MCJack123/PSG/images/image1.jpg

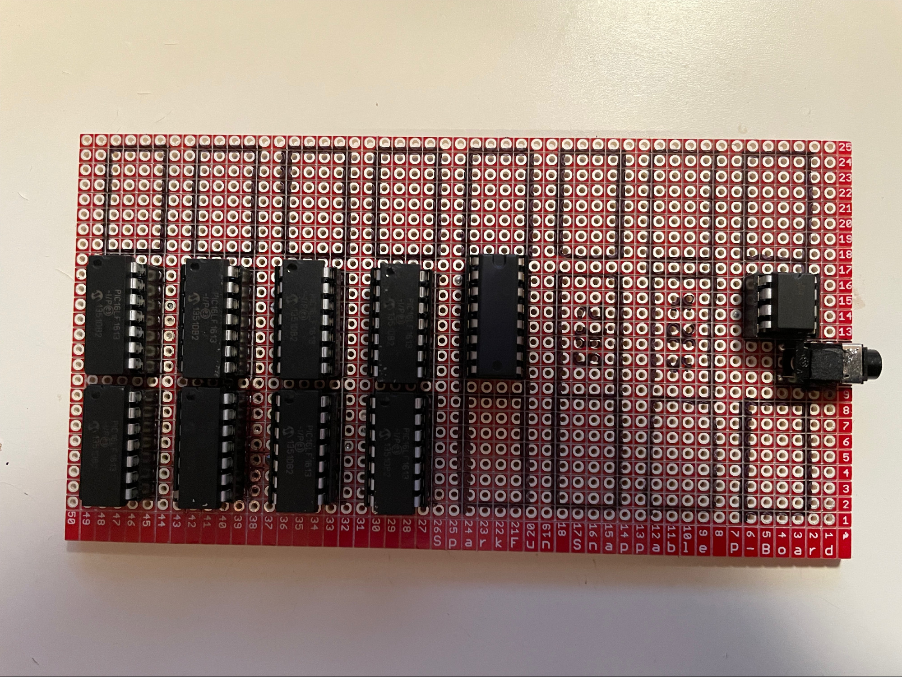
images/image1.jpg
