MCJack123/PSG/images/image2.jpg

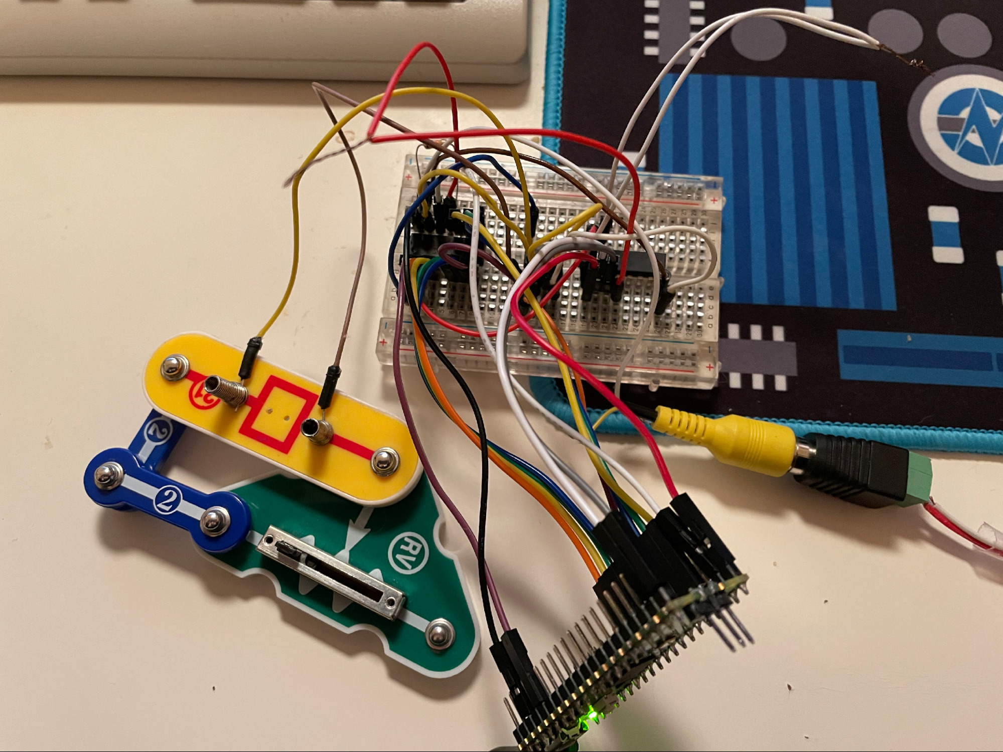
images/image2.jpg
