MCJack123/PSG/images/image4.jpg

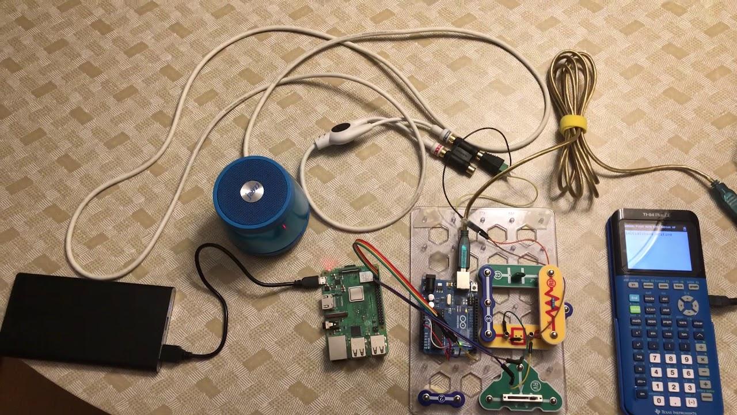
images/image4.jpg
