MCJack123/PSG/images/image5.jpg

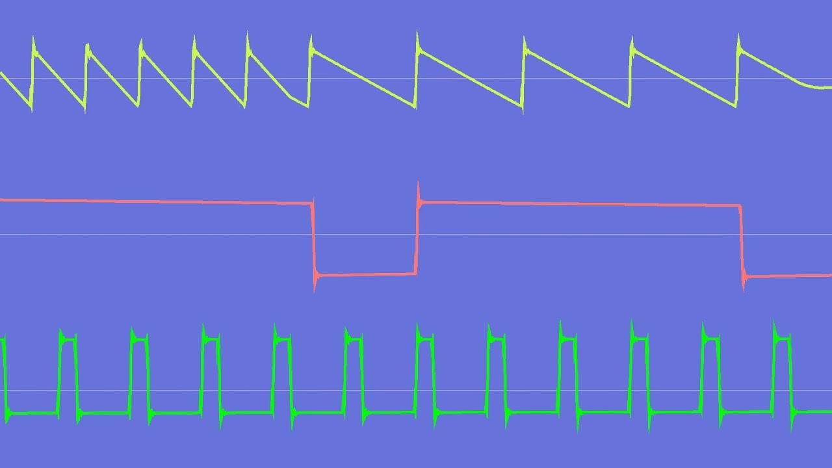
images/image5.jpg
