MCJack123/PSG/images/image6.jpg

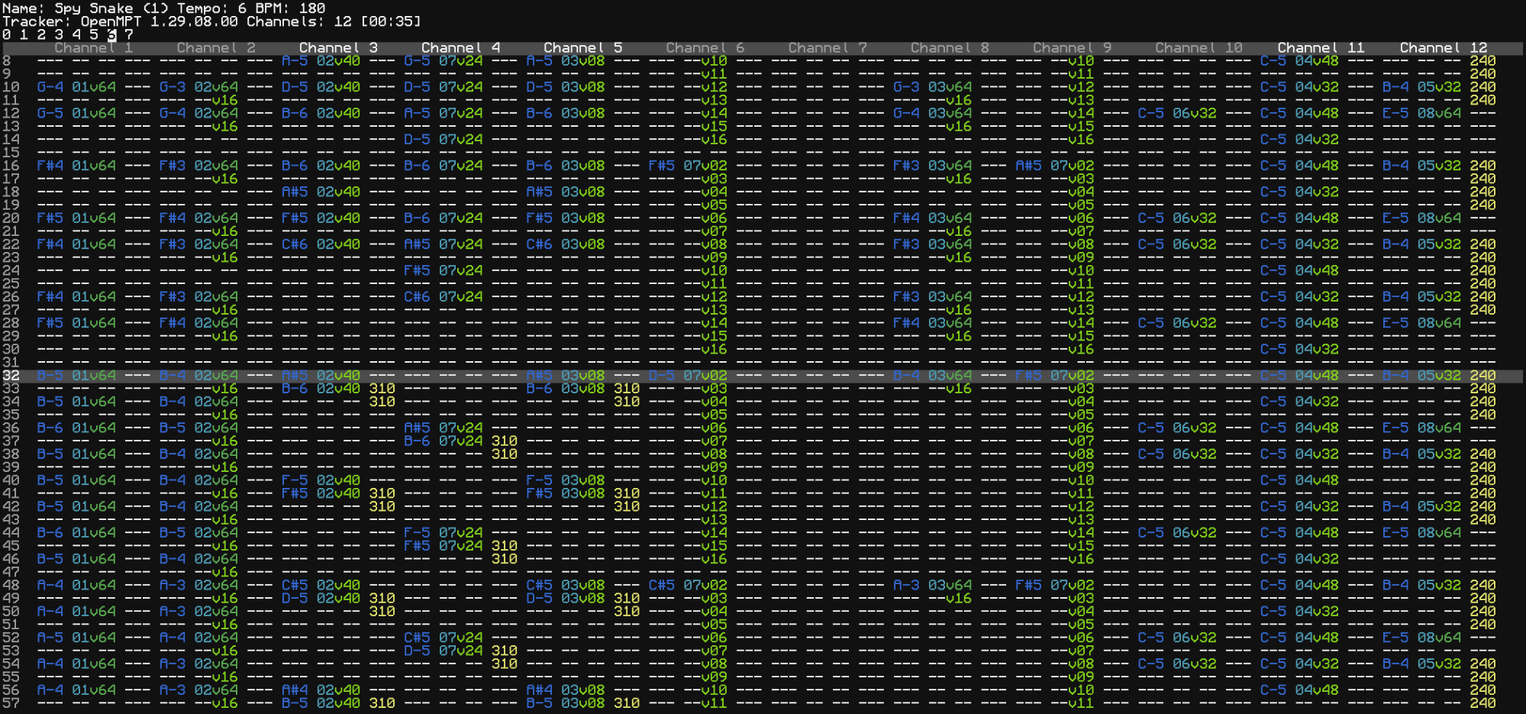
images/image6.jpg
