MCJack123/PSG/images/image7.jpg

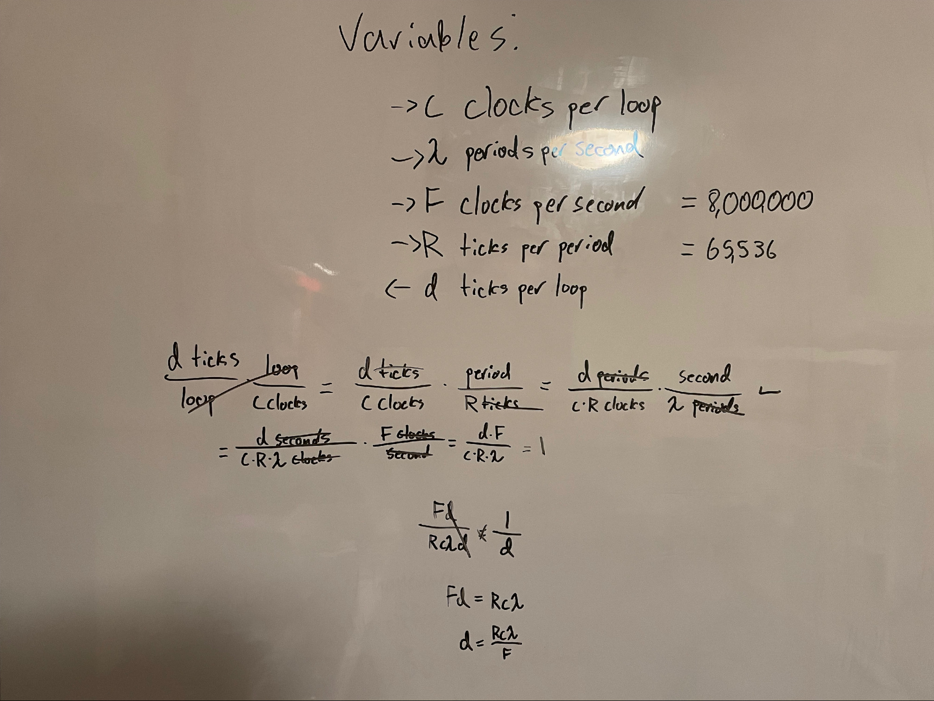
images/image7.jpg
