MCJack123/PSG/images/image8.jpg

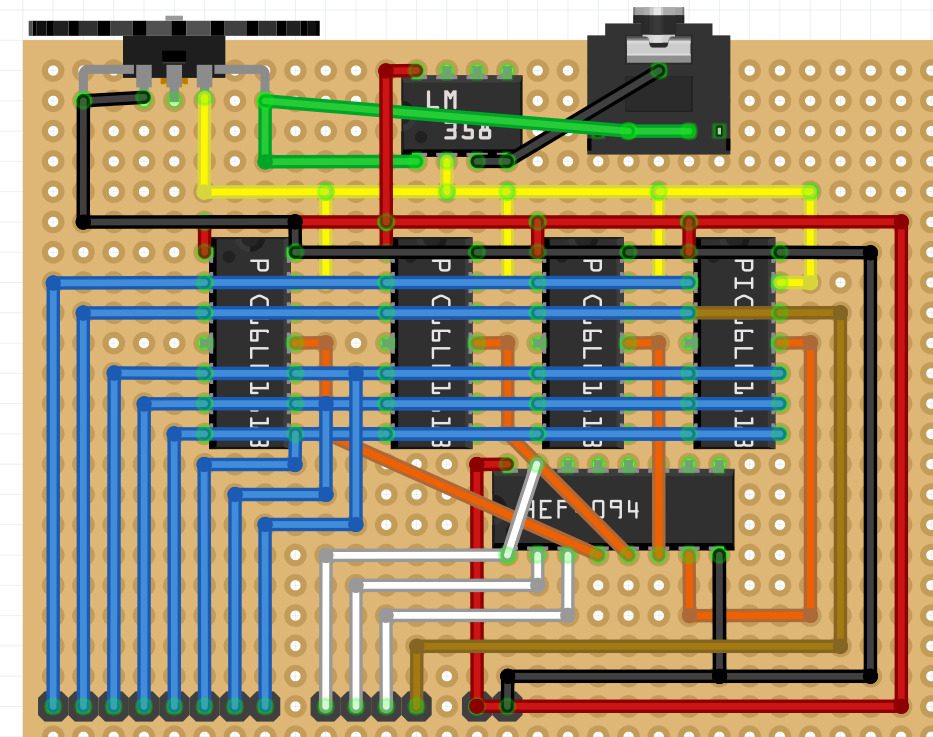
images/image8.jpg
