MCJack123/PSG/part-2/images/image1.png

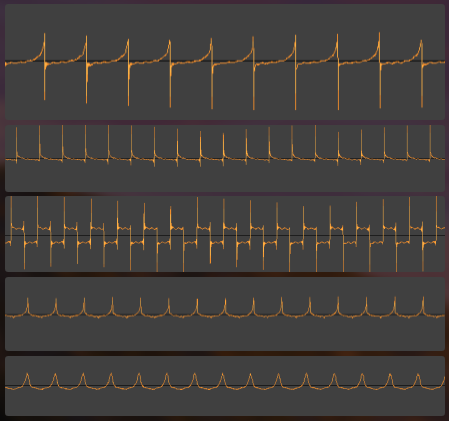
part-2/images/image1.png
