MCJack123/PSG/part-2/images/image2.jpg

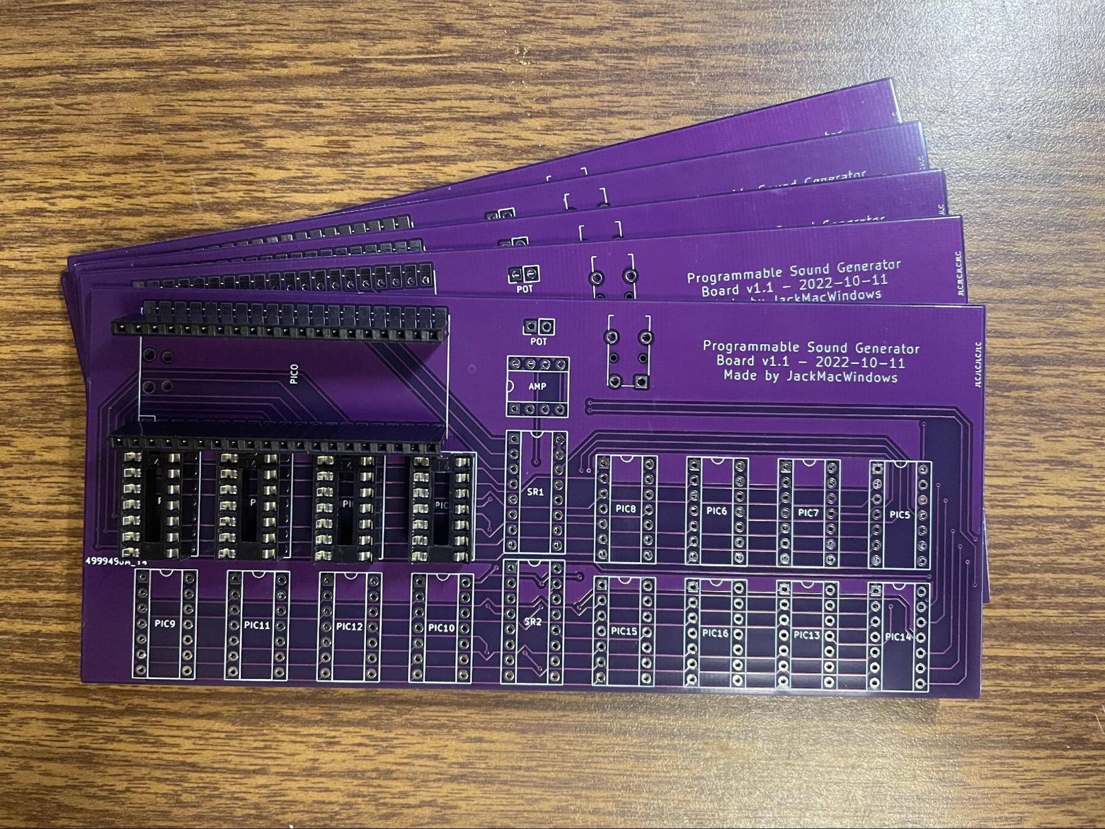
part-2/images/image2.jpg
