MCJack123/PSG/part-2/images/image3.jpg

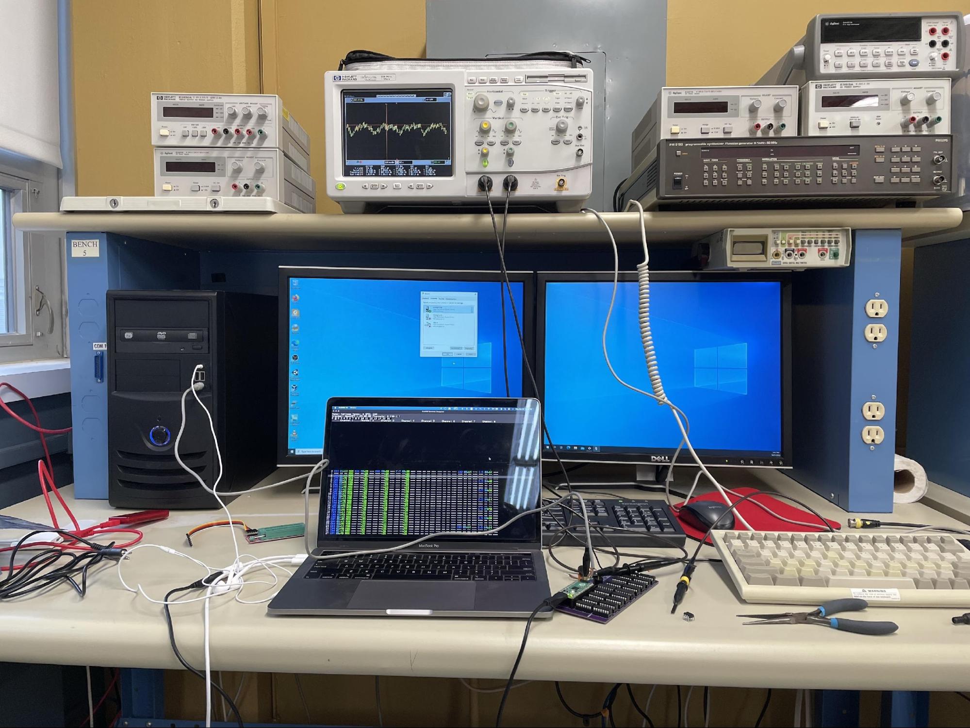
part-2/images/image3.jpg
