MCJack123/PSG/part-2/images/image4.png

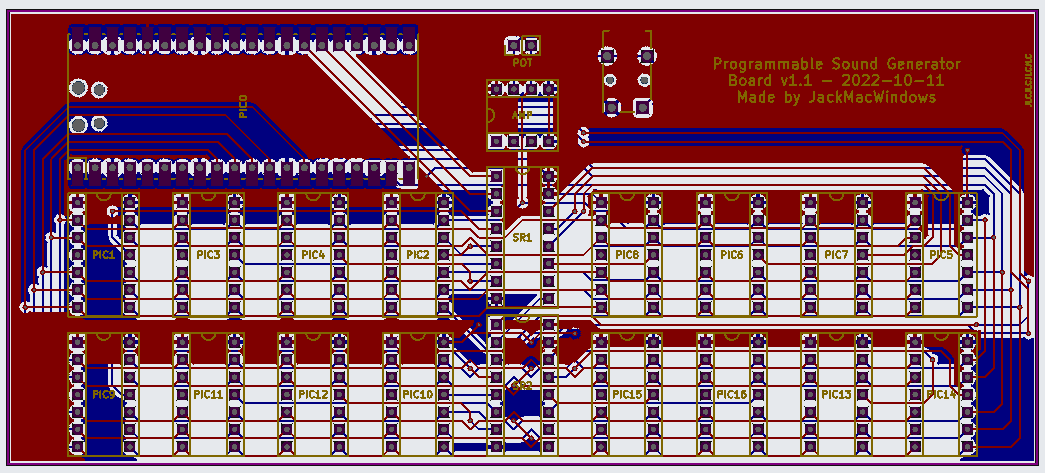
part-2/images/image4.png
