MCJack123/PSG/part-2/images/image5.jpg

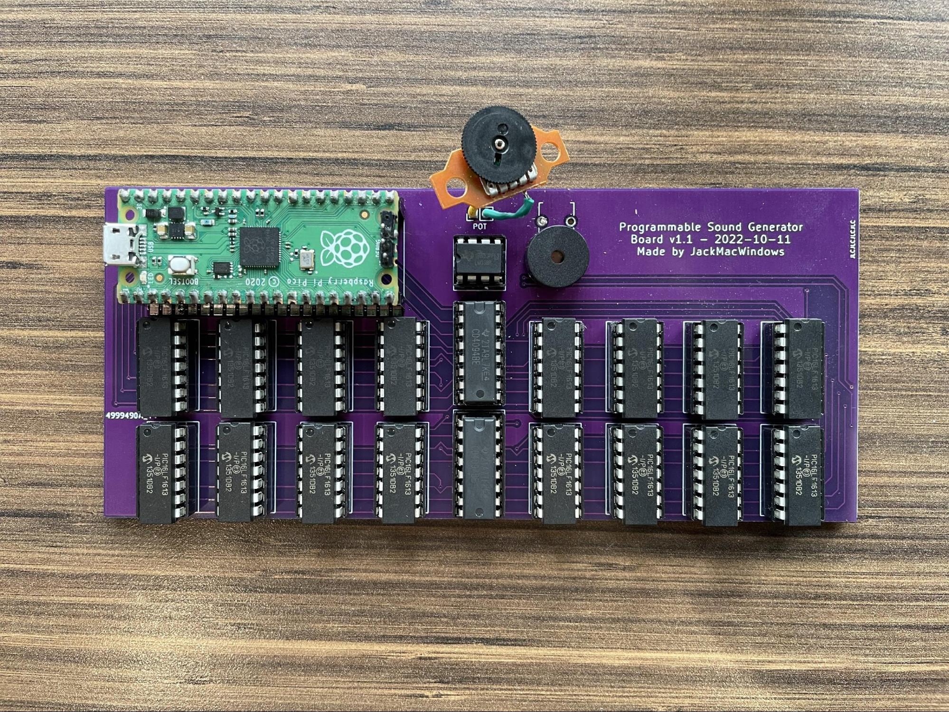
part-2/images/image5.jpg
